stevenbennett/Open-Task-Light/Open Task Light/Printed Parts/STEP/Power Tracks/power-track-support-alt-thinner(2.45)_v1.0.step

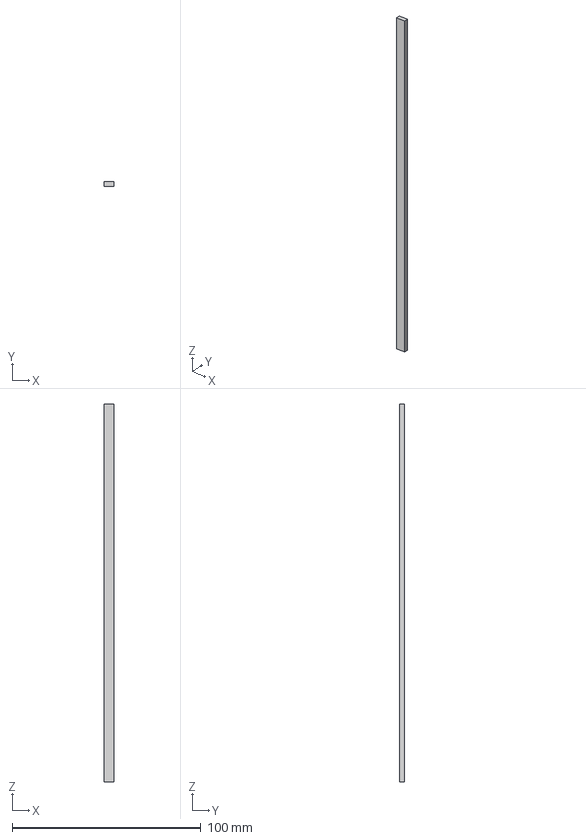
[picture p15: CAD file, 2026-08-29]
Open Task Light/Printed Parts/STEP/Power Tracks/power-track-support-alt-thinner(2.45)_v1.0.step
5.50 x 2.45 x 200.0 mm
