stevenbennett/Open-Task-Light/Open Task Light/Printed Parts/STEP/Rail Ends/pulley-mount_v1.0.step

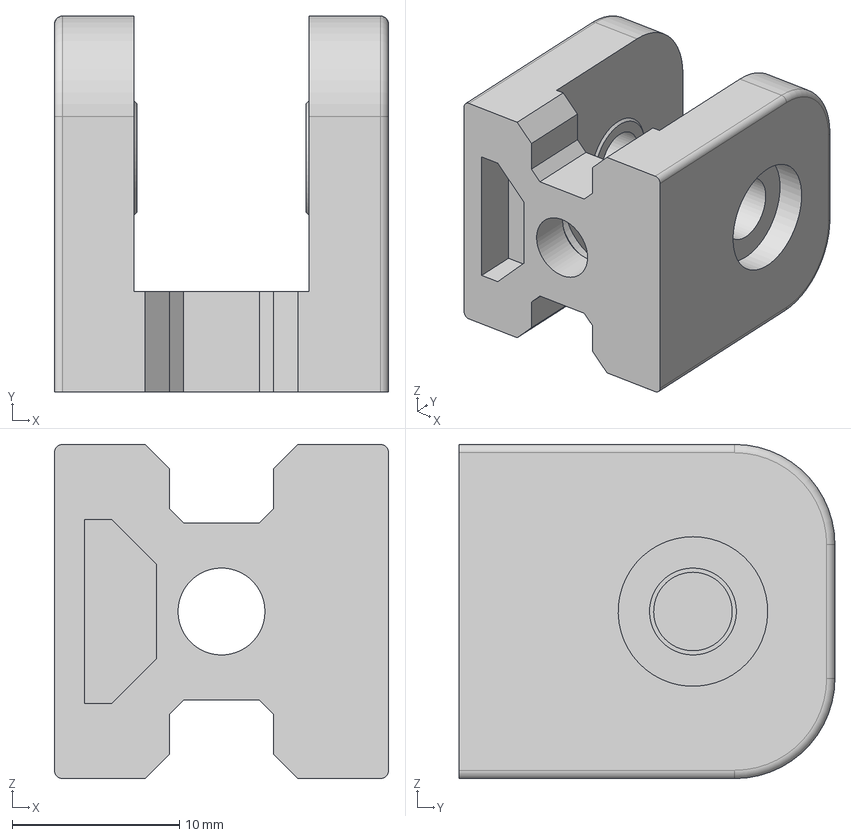
[picture p16: CAD file, 2026-08-29]
Open Task Light/Printed Parts/STEP/Rail Ends/pulley-mount_v1.0.step
20.0 x 22.5 x 20.0 mm
