stevenbennett/Open-Task-Light/Open Task Light/Printed Parts/STEP/Tools/hardware-fit-tester_v1.0.step

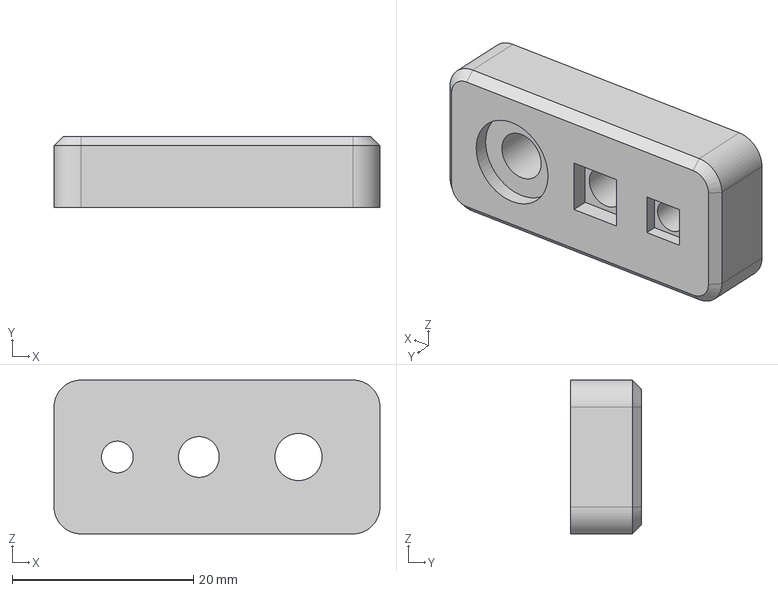
[picture p17: CAD file, 2026-09-07]
Open Task Light/Printed Parts/STEP/Tools/hardware-fit-tester_v1.0.step
36.0 x 7.80 x 17.0 mm
