stevenbennett/Open-Task-Light/Open Task Light Express/Community-Made Alternatives/jfuchs - Gimbal/Extrusion bracket.stl

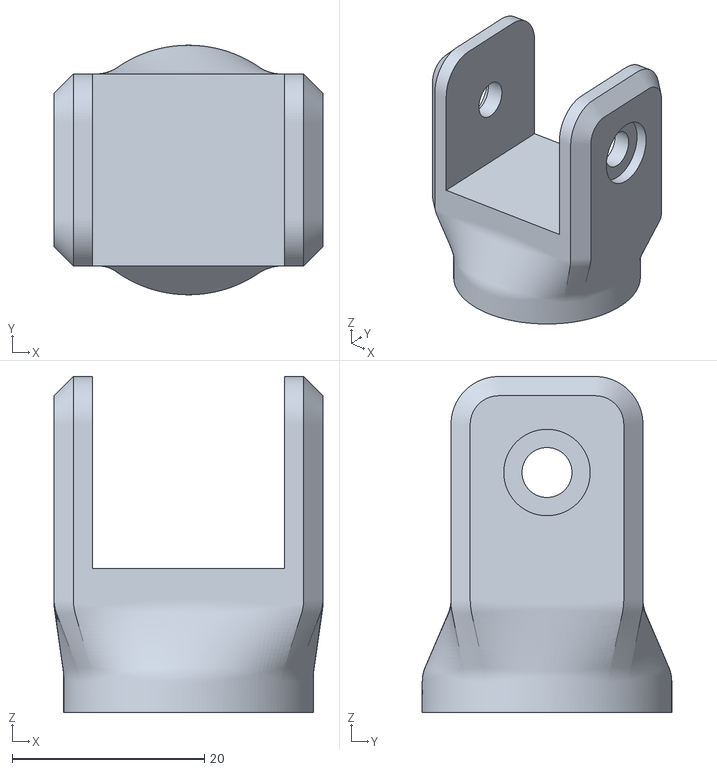
[picture p18: CAD file, 2025-07-02]
Open Task Light Express/Community-Made Alternatives/jfuchs - Gimbal/Extrusion bracket.stl
28.0 x 26.0 x 35.0
