stevenbennett/Open-Task-Light/Open Task Light Express/Community-Made Alternatives/tobias -> led holder -> neewer tl96/neewer_holder.step

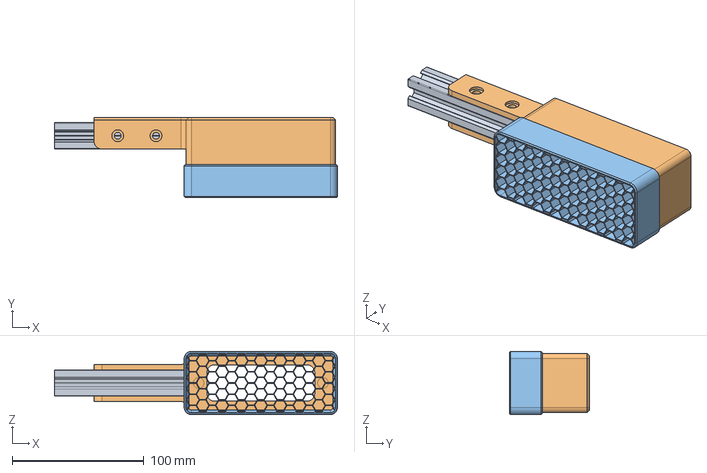
[picture p19: CAD file, 2025-07-01]
Open Task Light Express/Community-Made Alternatives/tobias -> led holder -> neewer tl96/neewer_holder.step
215.0 x 61.0 x 48.0 mm
Rail
neewer L2
