stevenbennett/Open-Task-Light/Open Task Light/Printed Parts/STEP/_Included in Kit/electronics-housing-ambient-light-window_v1.0.step

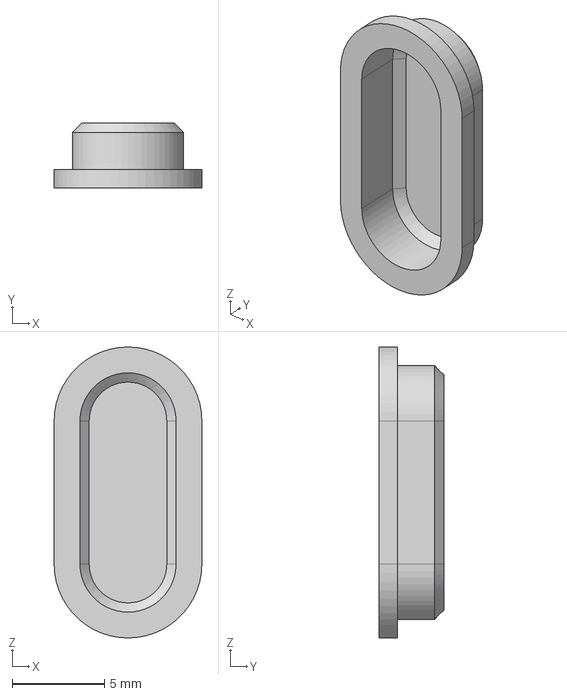
[picture p20: CAD file, 2026-08-29]
Open Task Light/Printed Parts/STEP/_Included in Kit/electronics-housing-ambient-light-window_v1.0.step
8.00 x 3.50 x 15.8 mm
