stevenbennett/Open-Task-Light/Open Task Light/Printed Parts/STEP/_Self-sourcing Tools/Heat Pipe Clamp.step

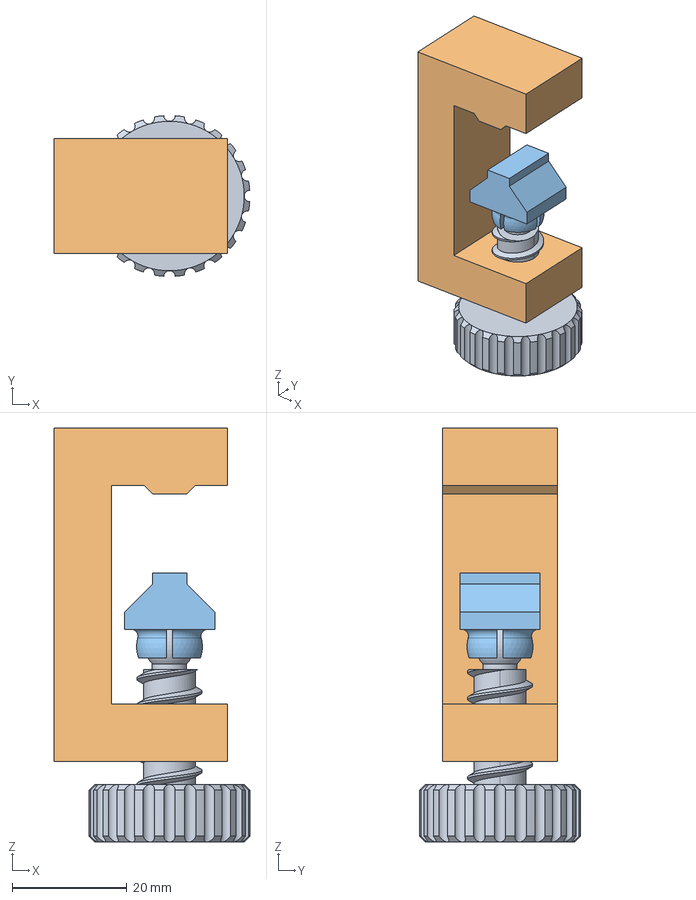
[picture p21: CAD file, 2026-09-11]
Open Task Light/Printed Parts/STEP/_Self-sourcing Tools/Heat Pipe Clamp.step
34.0 x 27.9 x 72.0 mm
Pin
Clamp Body
Tip
