stevenbennett/Open-Task-Light/Open Task Light/Printed Parts/STEP/Carriage/carriage-body_v1.1.step

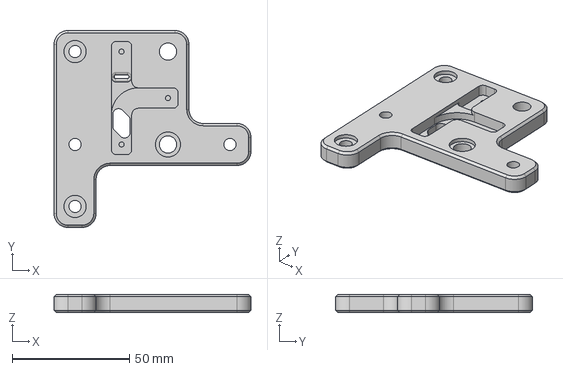
[picture p22: CAD file, 2026-08-29]
Open Task Light/Printed Parts/STEP/Carriage/carriage-body_v1.1.step
84.2 x 84.2 x 7.80 mm
