stevenbennett/Open-Task-Light/Open Task Light/Printed Parts/STEP/Clamping Base/clamping-base-power-plug-clip_v1.0.step

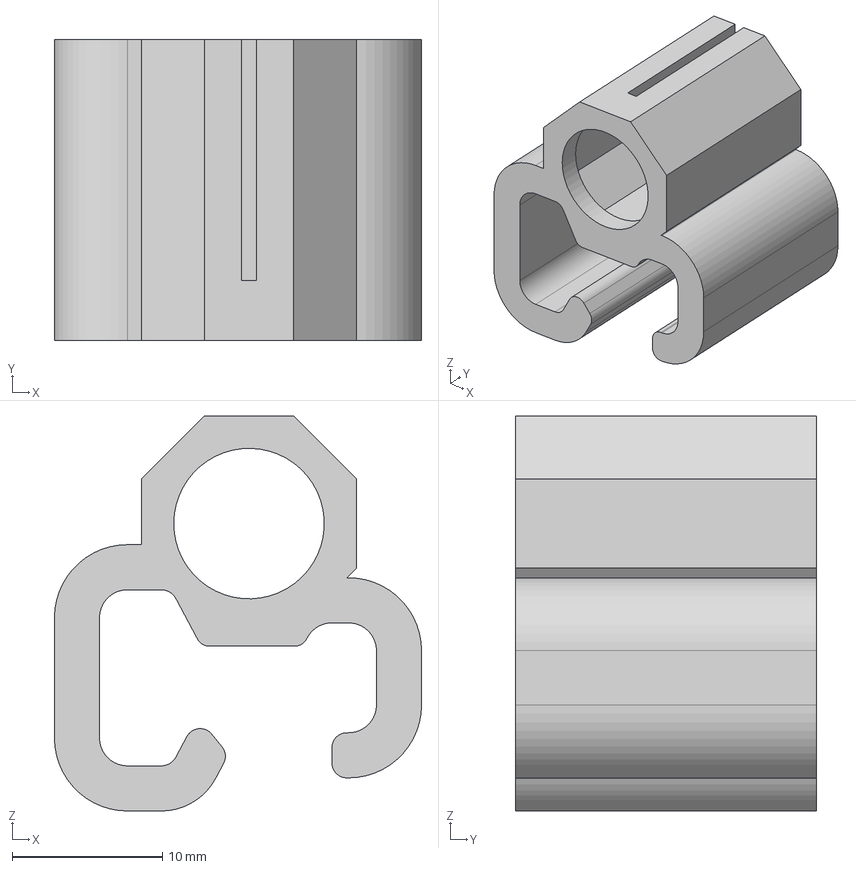
[picture p23: CAD file, 2026-08-29]
Open Task Light/Printed Parts/STEP/Clamping Base/clamping-base-power-plug-clip_v1.0.step
24.4 x 20.0 x 26.3 mm
