stevenbennett/Open-Task-Light/Open Task Light/Printed Parts/STEP/Counterweight/counterweight-belt-clip_v1.0.step

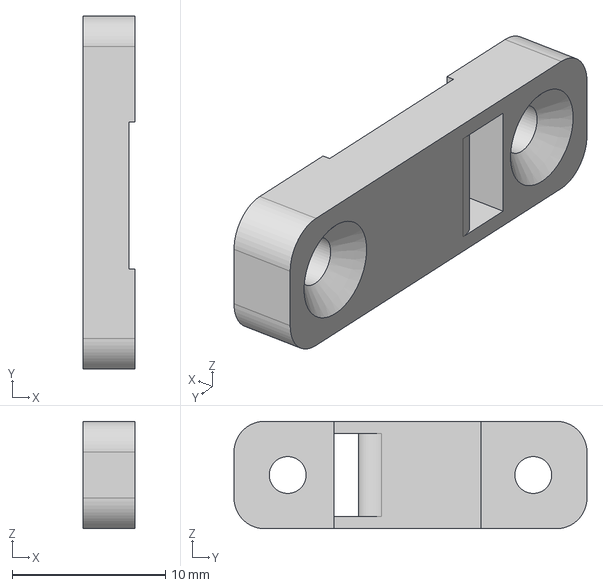
[picture p24: CAD file, 2026-08-29]
Open Task Light/Printed Parts/STEP/Counterweight/counterweight-belt-clip_v1.0.step
3.40 x 23.0 x 7.00 mm
