stevenbennett/Open-Task-Light/Open Task Light/Printed Parts/STEP/Electronics Housing/electronics-housing-button-sockets_v1.0.step

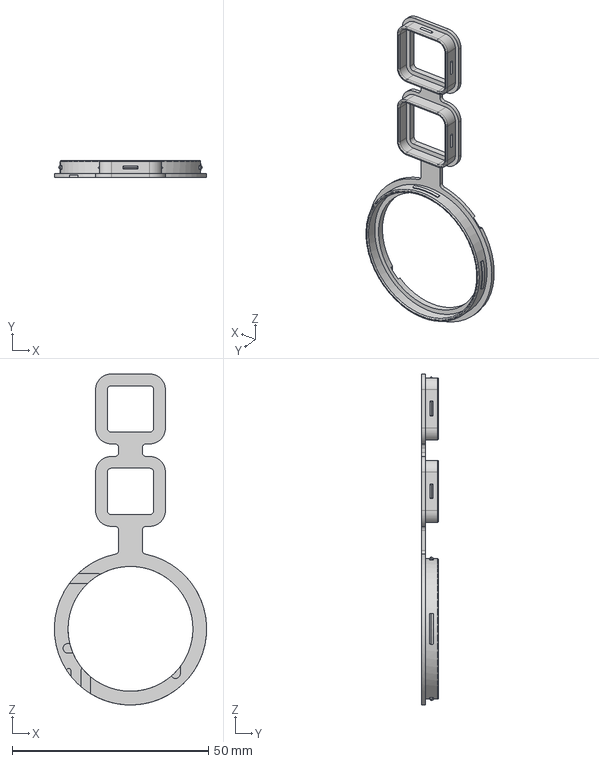
[picture p25: CAD file, 2026-08-29]
Open Task Light/Printed Parts/STEP/Electronics Housing/electronics-housing-button-sockets_v1.0.step
38.8 x 4.40 x 84.3 mm
