stevenbennett/Open-Task-Light/Open Task Light/Printed Parts/STEP/Freestanding Base/freestanding-base-outer-shell_v1.1.step

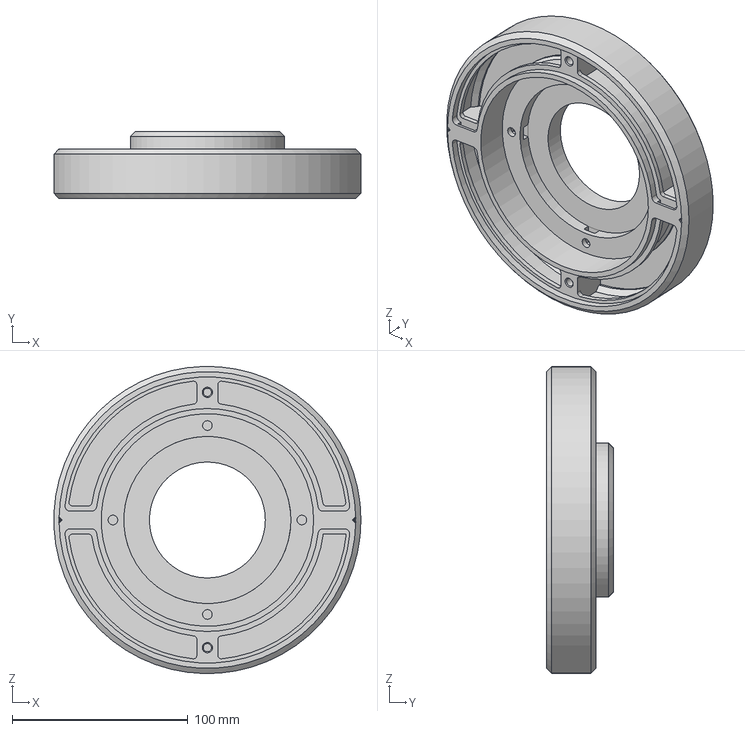
[picture p26: CAD file, 2026-09-16]
Open Task Light/Printed Parts/STEP/Freestanding Base/freestanding-base-outer-shell_v1.1.step
174.9 x 38.4 x 174.9 mm
