stevenbennett/Open-Task-Light/Open Task Light/Printed Parts/STEP/Power Tracks/power-track-support-alt-thicker(2.65)_v1.0.step

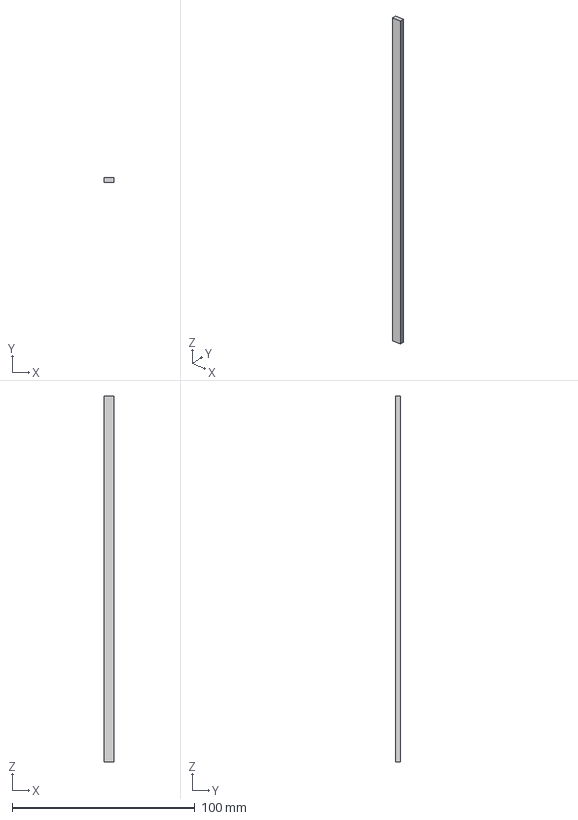
[picture p27: CAD file, 2026-08-29]
Open Task Light/Printed Parts/STEP/Power Tracks/power-track-support-alt-thicker(2.65)_v1.0.step
5.50 x 2.65 x 200.0 mm
