stevenbennett/Open-Task-Light/Open Task Light/Printed Parts/STEP/Rail Ends/rail-end-cap_v1.0.step

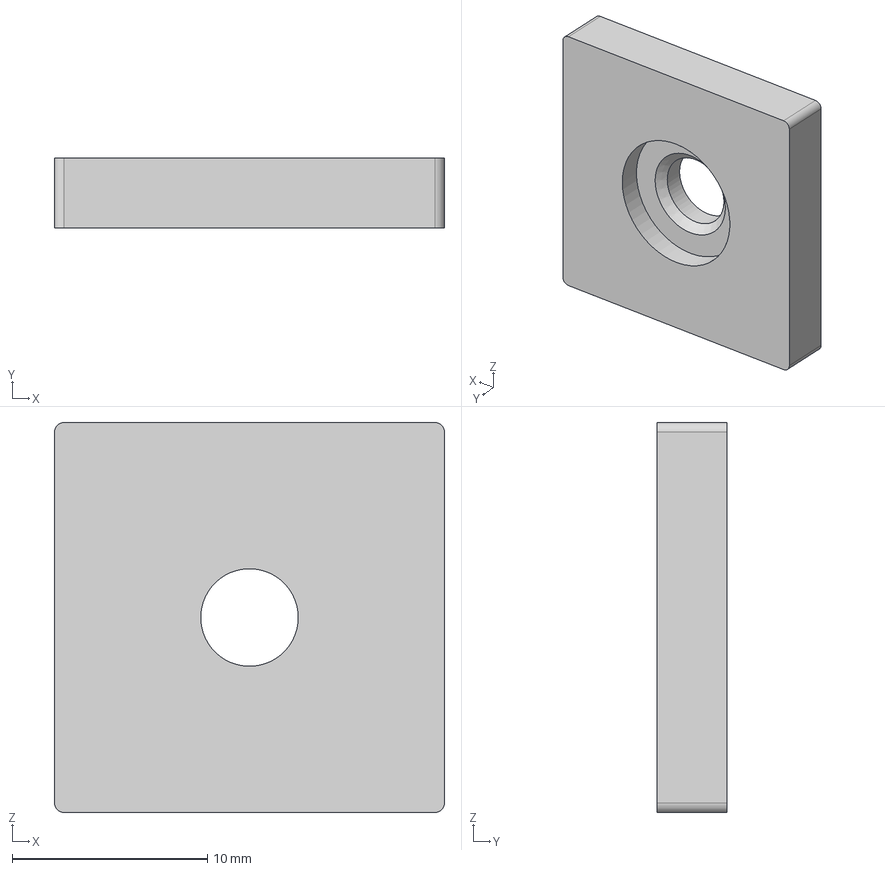
[picture p28: CAD file, 2026-08-29]
Open Task Light/Printed Parts/STEP/Rail Ends/rail-end-cap_v1.0.step
20.0 x 3.60 x 20.0 mm
