stevenbennett/Open-Task-Light/Open Task Light/Printed Parts/STEP/Tools/weight-material-scoop_v1.0.step

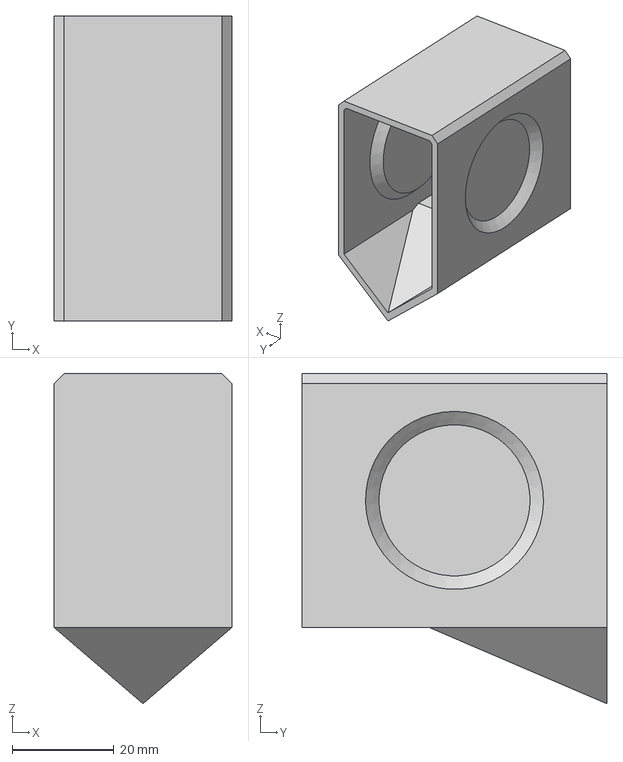
[picture p29: CAD file, 2026-08-29]
Open Task Light/Printed Parts/STEP/Tools/weight-material-scoop_v1.0.step
35.0 x 60.0 x 65.0 mm
