stevenbennett/Open-Task-Light/Open Task Light Express/Community-Made Alternatives/jfuchs - Gimbal/Inner ring.stl

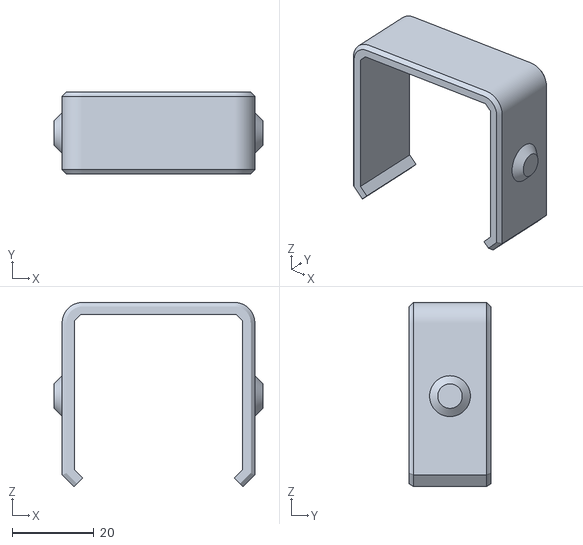
[picture p30: CAD file, 2025-07-02]
Open Task Light Express/Community-Made Alternatives/jfuchs - Gimbal/Inner ring.stl
51.2 x 20.0 x 45.1
