stevenbennett/Open-Task-Light/Open Task Light Express/Community-Made Alternatives/tobias -> led holder -> neewer tl96/neewer_tl96_holder.stl

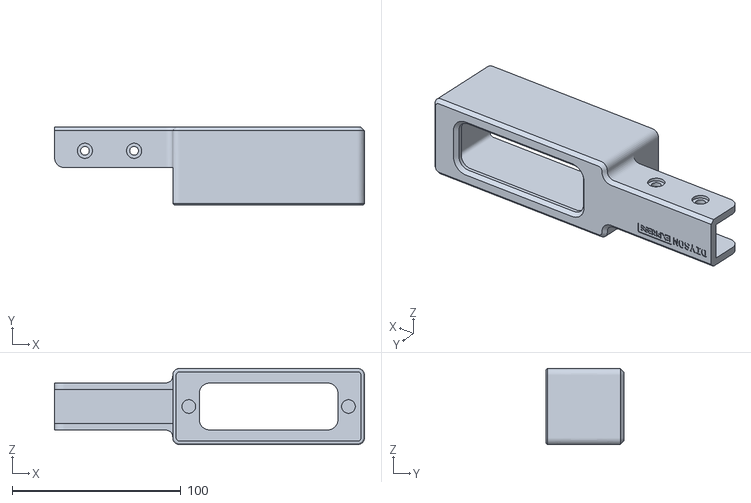
[picture p31: CAD file, 2025-07-01]
Open Task Light Express/Community-Made Alternatives/tobias -> led holder -> neewer tl96/neewer_tl96_holder.stl
183.5 x 46.0 x 45.0
