stevenbennett/Open-Task-Light/Open Task Light/Printed Parts/STEP/Clamping Base/clamping-base-rail-terminal_v1.0.step

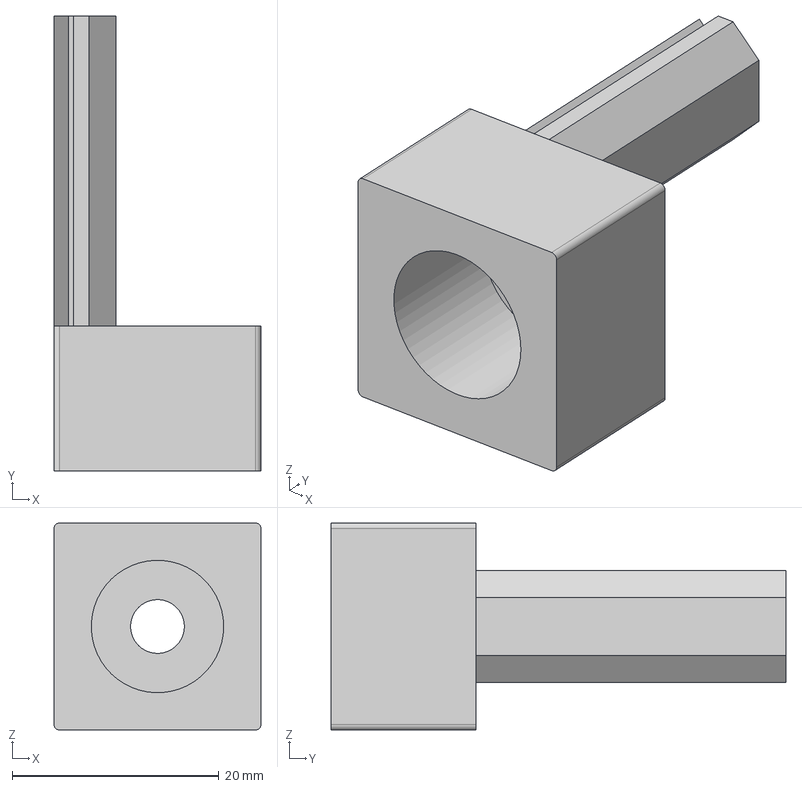
[picture p33: CAD file, 2026-08-29]
Open Task Light/Printed Parts/STEP/Clamping Base/clamping-base-rail-terminal_v1.0.step
20.0 x 44.0 x 20.0 mm
