stevenbennett/Open-Task-Light/Open Task Light/Printed Parts/STEP/Counterweight/counterweight-lid-steel_v1.0.step

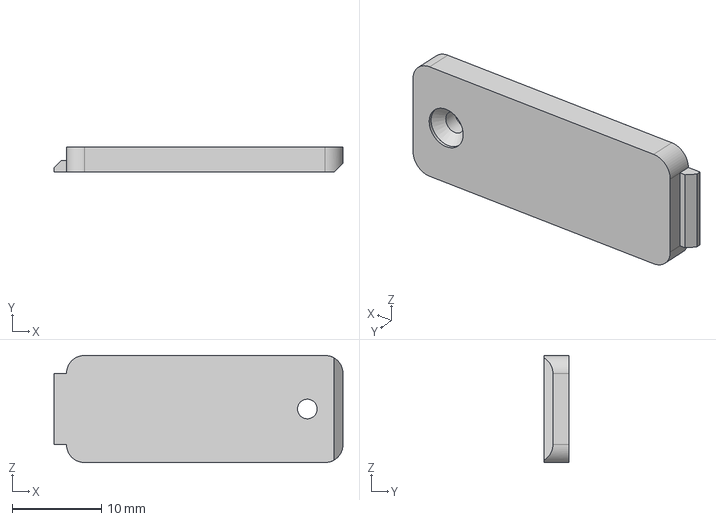
[picture p34: CAD file, 2026-08-29]
Open Task Light/Printed Parts/STEP/Counterweight/counterweight-lid-steel_v1.0.step
32.4 x 2.80 x 12.0 mm
