stevenbennett/Open-Task-Light/Open Task Light/Printed Parts/STEP/Electronics Housing/electronics-housing-shade_v1.0.step

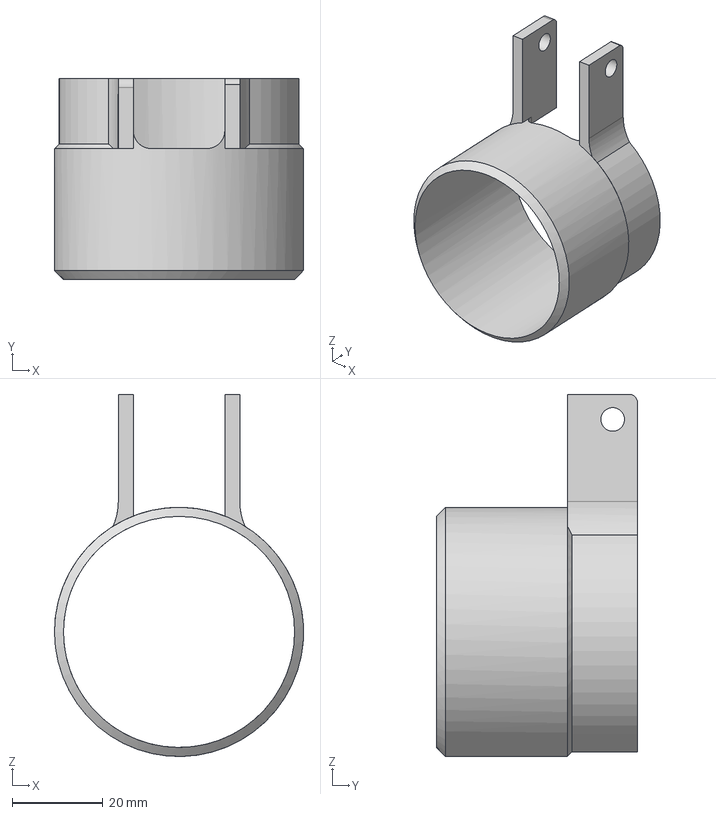
[picture p35: CAD file, 2026-08-29]
Open Task Light/Printed Parts/STEP/Electronics Housing/electronics-housing-shade_v1.0.step
55.0 x 44.4 x 79.9 mm
