stevenbennett/Open-Task-Light/Open Task Light/Printed Parts/STEP/Freestanding Base/freestanding-base-bottom-shell-lid_v1.1.step

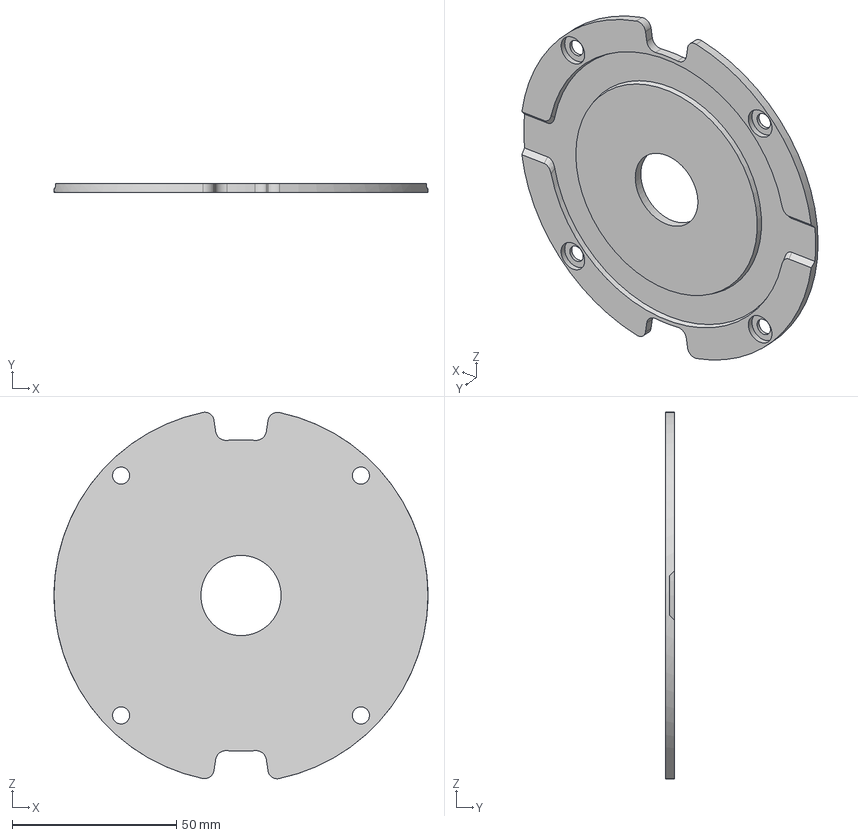
[picture p36: CAD file, 2026-09-16]
Open Task Light/Printed Parts/STEP/Freestanding Base/freestanding-base-bottom-shell-lid_v1.1.step
113.8 x 2.80 x 111.5 mm
