stevenbennett/Open-Task-Light/Open Task Light/Printed Parts/STEP/Rail Ends/pulley-mount-insert_v1.0.step

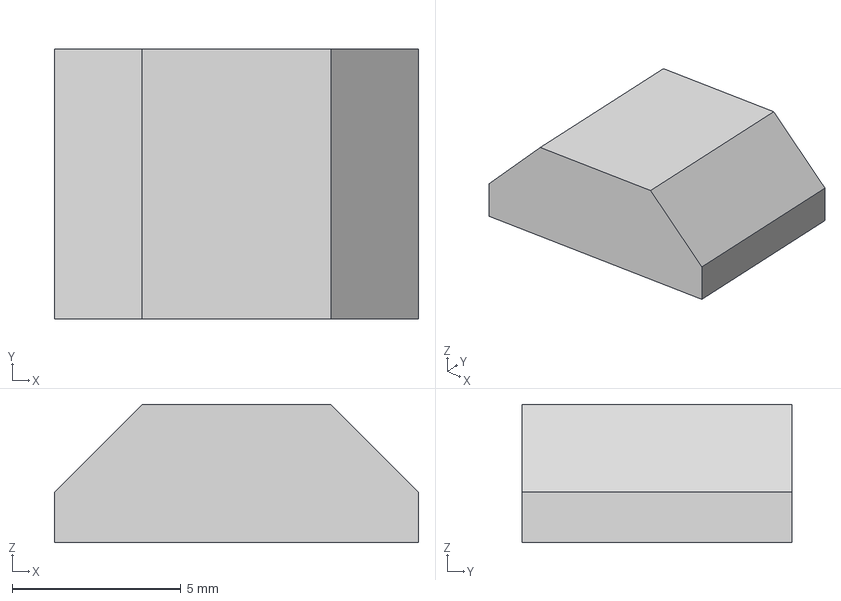
[picture p37: CAD file, 2026-08-29]
Open Task Light/Printed Parts/STEP/Rail Ends/pulley-mount-insert_v1.0.step
10.8 x 8.00 x 4.10 mm
