stevenbennett/Open-Task-Light/Open Task Light/Printed Parts/STEP/Tools/counterweight-funnel_v1.0.step

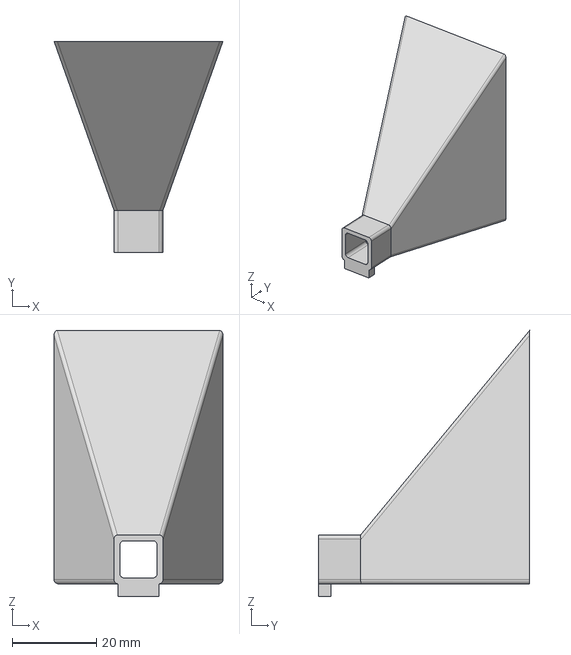
[picture p38: CAD file, 2026-08-29]
Open Task Light/Printed Parts/STEP/Tools/counterweight-funnel_v1.0.step
40.0 x 50.0 x 63.0 mm
