stevenbennett/Open-Task-Light/Open Task Light/Printed Parts/STEP/_Included in Kit/electronics-housing-power-button_v1.0.step

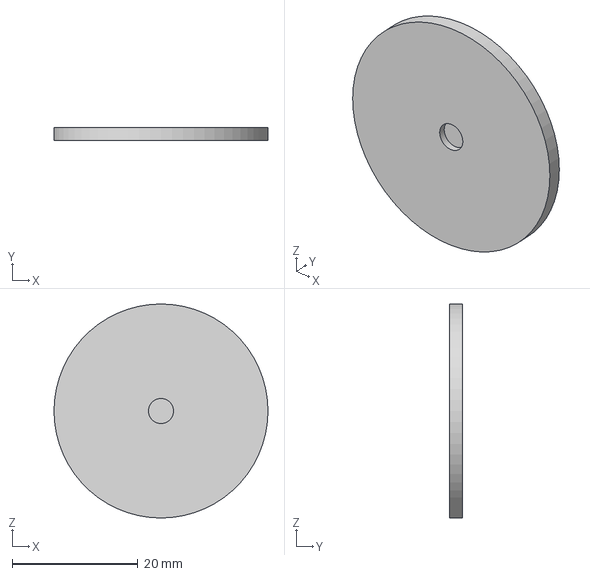
[picture p39: CAD file, 2026-08-29]
Open Task Light/Printed Parts/STEP/_Included in Kit/electronics-housing-power-button_v1.0.step
34.1 x 2.10 x 34.1 mm
