stevenbennett/Open-Task-Light/Open Task Light/Printed Parts/STEP/Counterweight/counterweight-enclosure-steel_v1.0.step

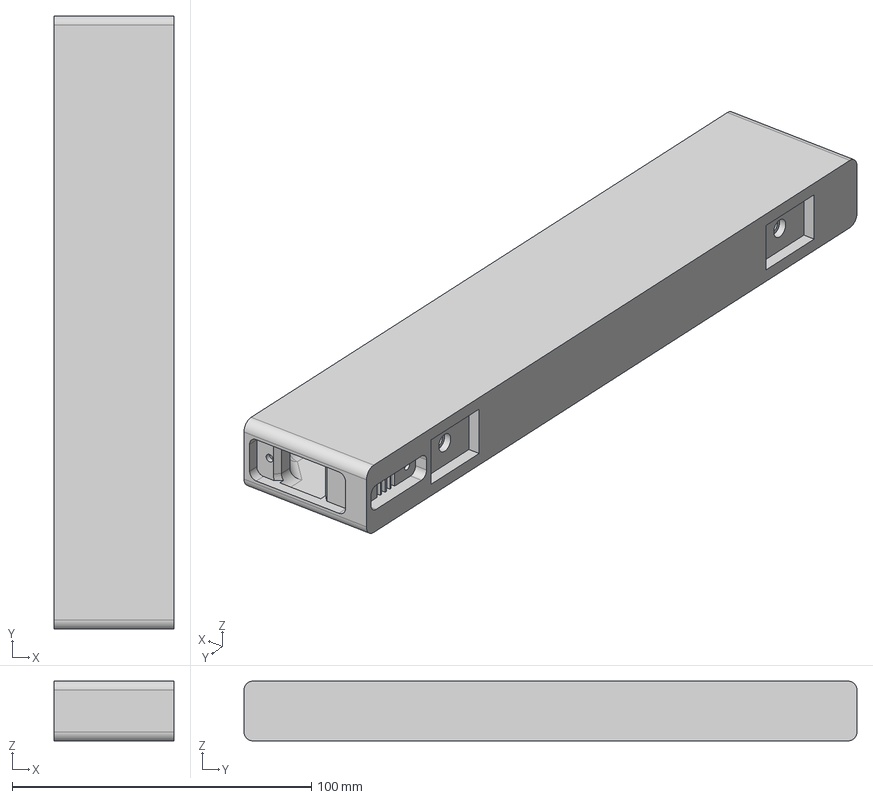
[picture p40: CAD file, 2026-08-29]
Open Task Light/Printed Parts/STEP/Counterweight/counterweight-enclosure-steel_v1.0.step
40.0 x 205.0 x 20.0 mm
