stevenbennett/Open-Task-Light/Open Task Light/Printed Parts/STEP/Freestanding Base/freestanding-base-bracket-cover_v1.1.step

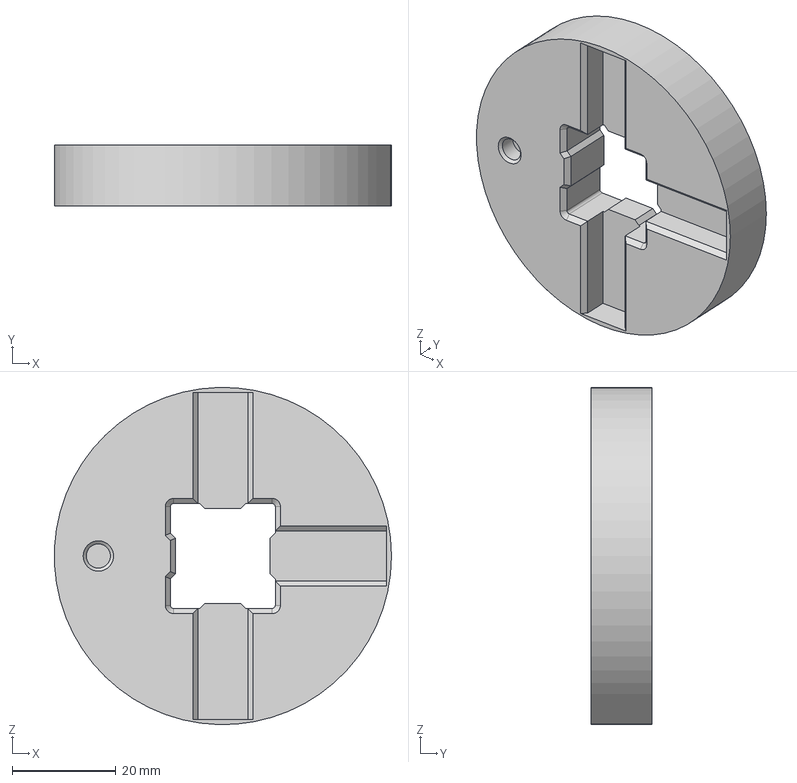
[picture p41: CAD file, 2026-09-16]
Open Task Light/Printed Parts/STEP/Freestanding Base/freestanding-base-bracket-cover_v1.1.step
65.0 x 11.8 x 65.0 mm
