stevenbennett/Open-Task-Light/Open Task Light/Printed Parts/STEP/Tools/power-track-offset-freestanding-base_v1.0.step

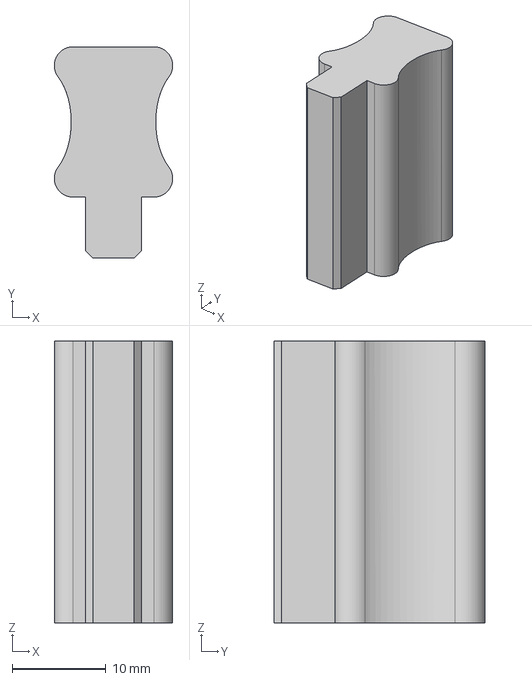
[picture p42: CAD file, 2026-08-29]
Open Task Light/Printed Parts/STEP/Tools/power-track-offset-freestanding-base_v1.0.step
12.6 x 22.5 x 30.0 mm
