stevenbennett/Open-Task-Light/Open Task Light/Printed Parts/STEP/_Included in Kit/electronics-housing-pcb-clip_v1.0.step

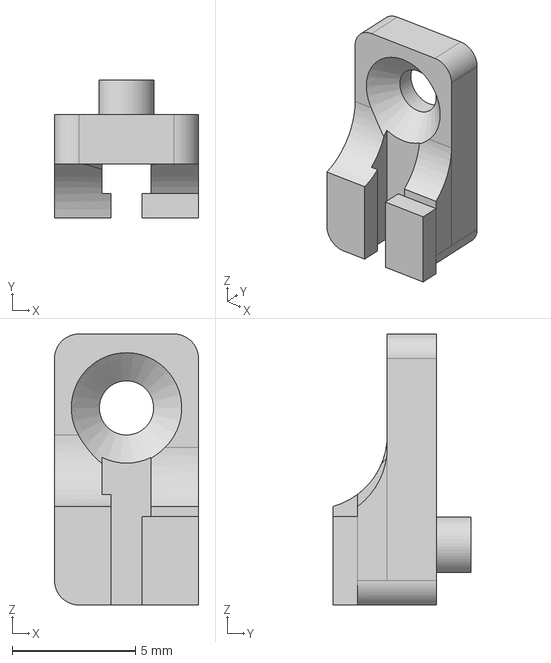
[picture p43: CAD file, 2026-08-29]
Open Task Light/Printed Parts/STEP/_Included in Kit/electronics-housing-pcb-clip_v1.0.step
5.85 x 5.60 x 11.0 mm
