stevenbennett/Open-Task-Light/Open Task Light/Printed Parts/STEP/Counterweight/counterweight-enclosure-lead_v1.0.step

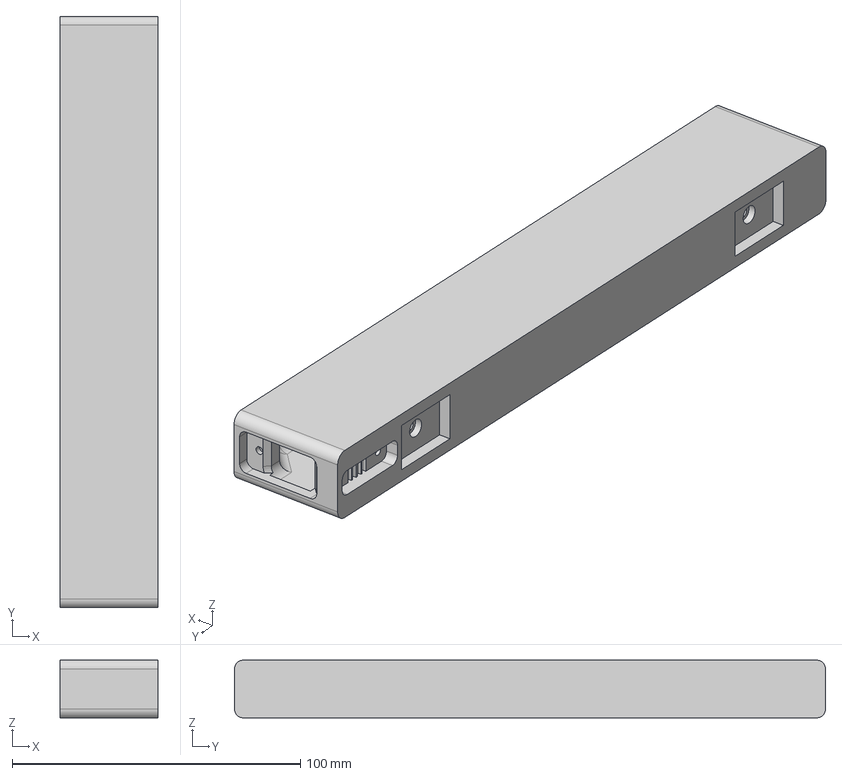
[picture p44: CAD file, 2026-08-29]
Open Task Light/Printed Parts/STEP/Counterweight/counterweight-enclosure-lead_v1.0.step
34.0 x 205.0 x 20.0 mm
