stevenbennett/Open-Task-Light/Open Task Light/Printed Parts/STEP/_Included in Kit/electronics-housing-decrease-brightness-button_v1.0.step

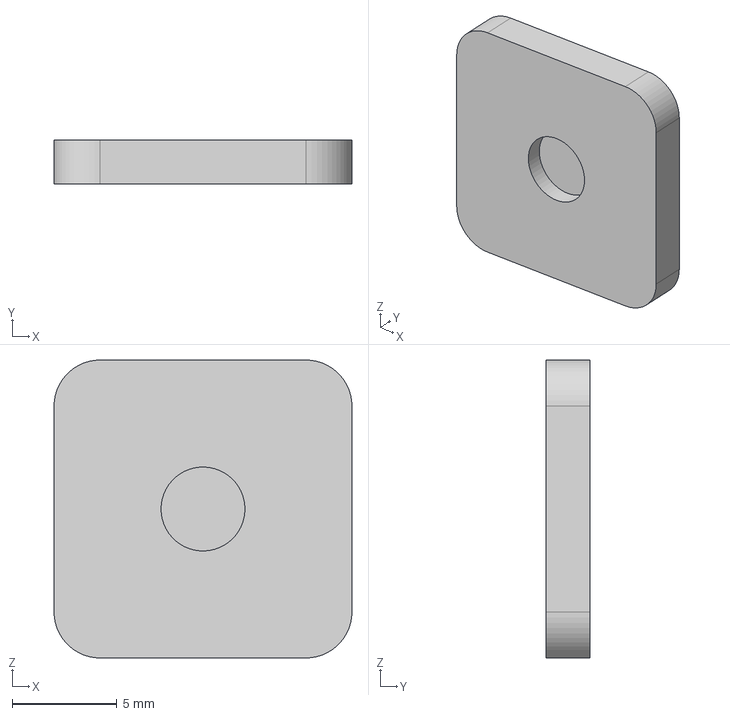
[picture p46: CAD file, 2026-08-29]
Open Task Light/Printed Parts/STEP/_Included in Kit/electronics-housing-decrease-brightness-button_v1.0.step
14.2 x 2.10 x 14.2 mm
