stevenbennett/Open-Task-Light/Open Task Light/Printed Parts/STEP/Freestanding Base/freestanding-base-bottom-shell_v1.1.step

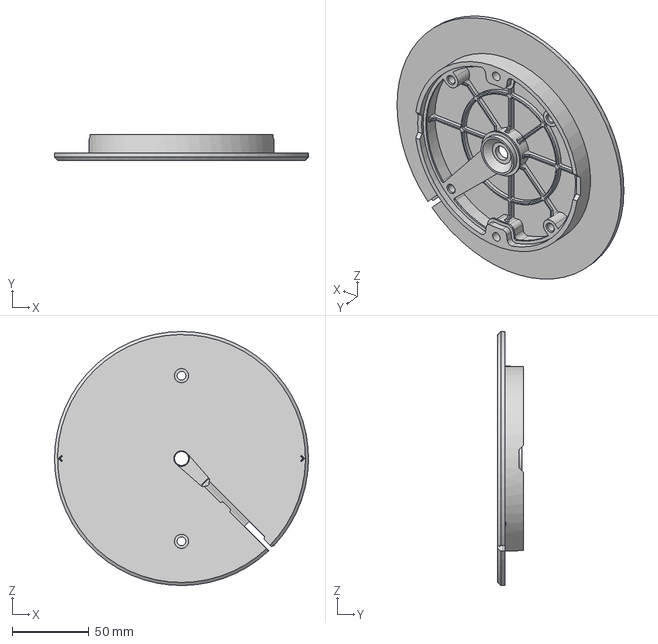
[picture p47: CAD file, 2026-08-29]
Open Task Light/Printed Parts/STEP/Freestanding Base/freestanding-base-bottom-shell_v1.1.step
165.0 x 16.6 x 165.0 mm
