stevenbennett/Open-Task-Light/Open Task Light/Printed Parts/STEP/_Included in Kit/counterweight-flex-tab_v1.0.step

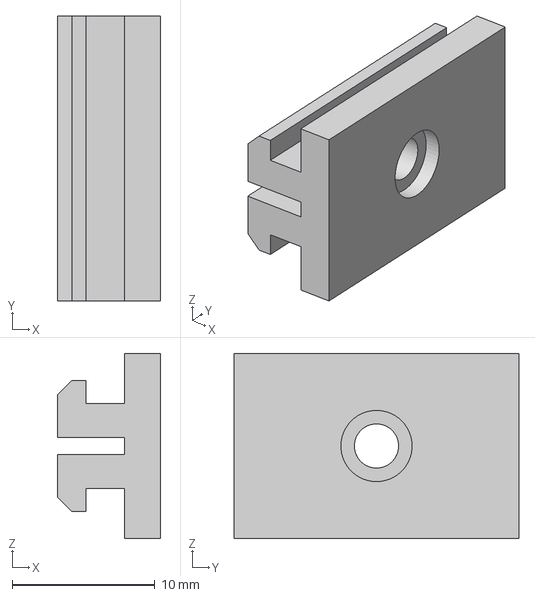
[picture p48: CAD file, 2026-08-29]
Open Task Light/Printed Parts/STEP/_Included in Kit/counterweight-flex-tab_v1.0.step
7.20 x 20.0 x 13.0 mm
