stevenbennett/Open-Task-Light/Open Task Light/Printed Parts/STEP/Freestanding Base/freestanding-base-bracket-plate_v1.0.step

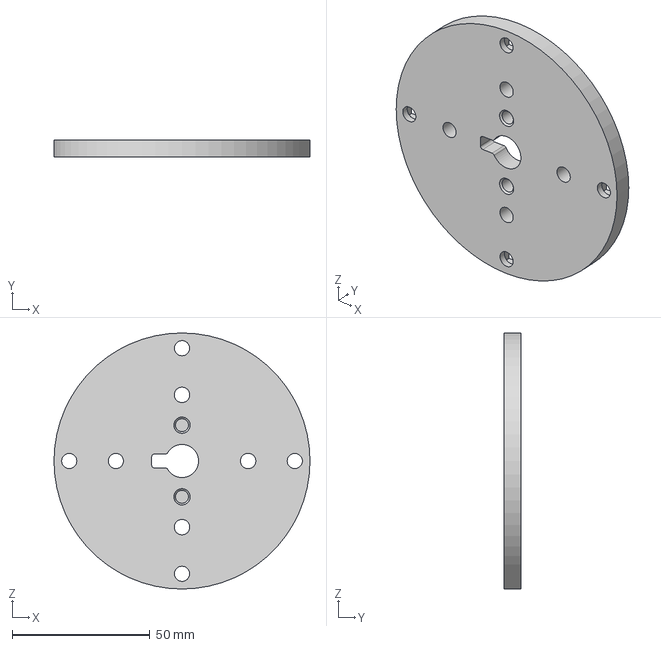
[picture p49: CAD file, 2026-08-29]
Open Task Light/Printed Parts/STEP/Freestanding Base/freestanding-base-bracket-plate_v1.0.step
92.9 x 6.35 x 92.9 mm
