stevenbennett/Open-Task-Light/Open Task Light/Printed Parts/STEP/_Included in Kit/freestanding-base-power-cable-cap_v1.0.step

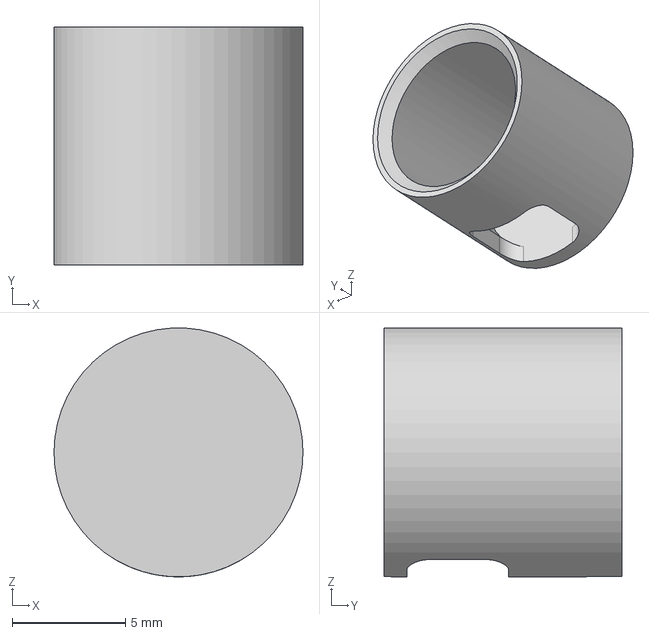
[picture p50: CAD file, 2026-08-29]
Open Task Light/Printed Parts/STEP/_Included in Kit/freestanding-base-power-cable-cap_v1.0.step
11.0 x 10.5 x 11.0 mm
