stevenbennett/Open-Task-Light/Open Task Light/Printed Parts/STEP/Freestanding Base/freestanding-base-power-jack-plate_v1.0.step

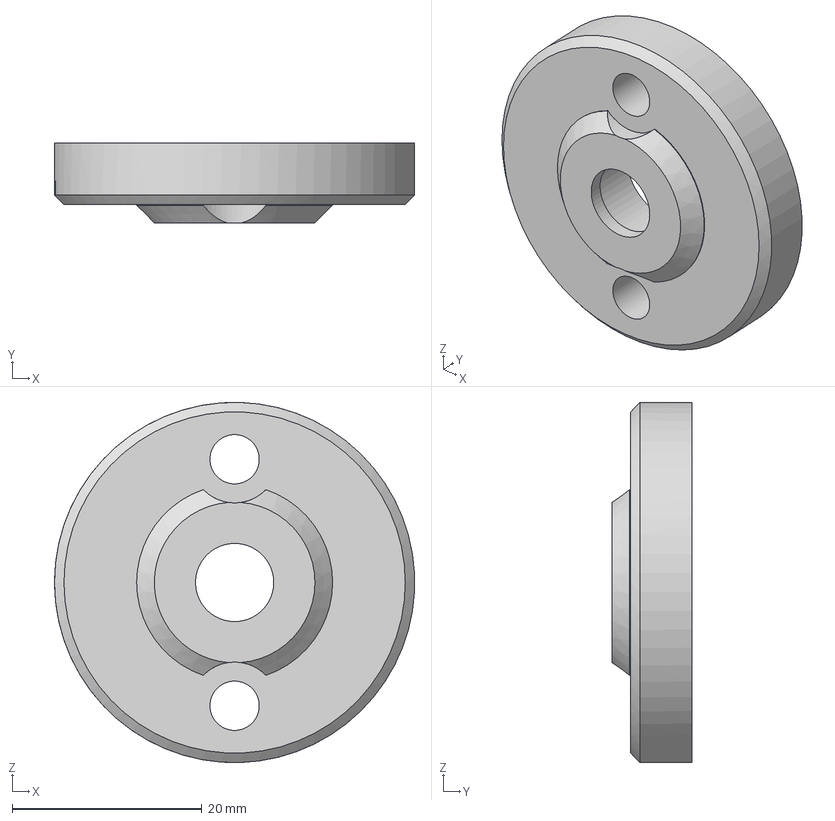
[picture p51: CAD file, 2026-08-29]
Open Task Light/Printed Parts/STEP/Freestanding Base/freestanding-base-power-jack-plate_v1.0.step
38.0 x 8.45 x 38.0 mm
